Remi-C/modern_captain_bed/images/build_book_nomenclature/2015-09-30_09-45-54.png

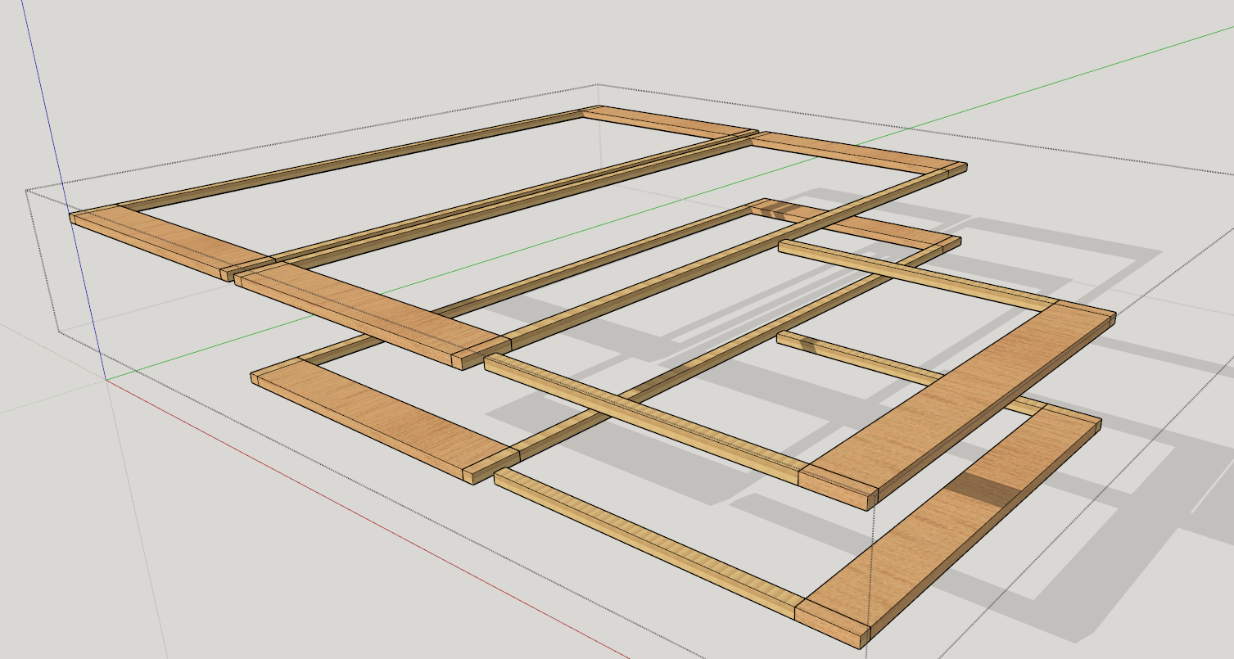
images/build_book_nomenclature/2015-09-30_09-45-54.png
