Remi-C/modern_captain_bed/images/build_book_nomenclature/A_2.png

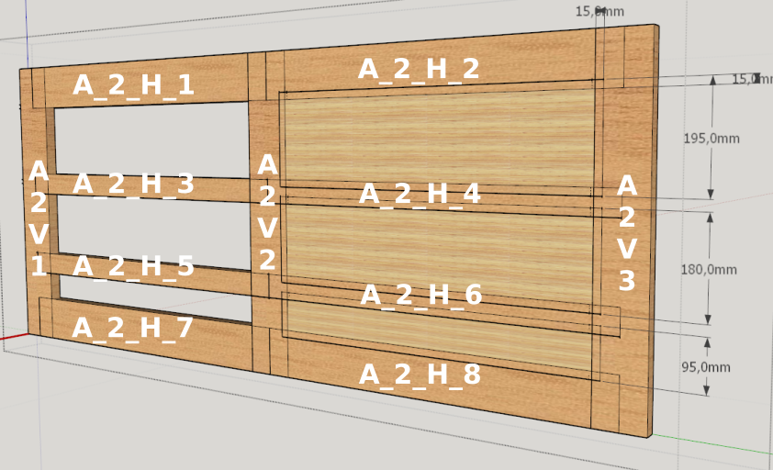
images/build_book_nomenclature/A_2.png
