Remi-C/modern_captain_bed/images/build_book_nomenclature/A_P_G.png

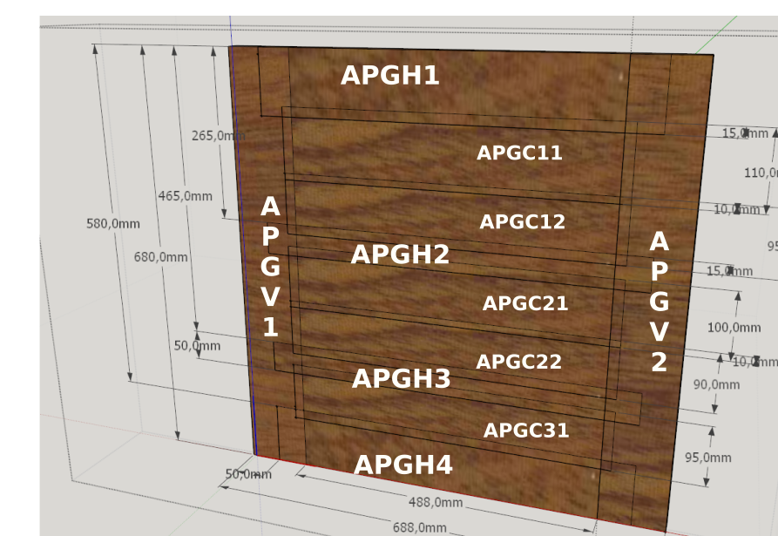
images/build_book_nomenclature/A_P_G.png
