Remi-C/modern_captain_bed/images/build_book_nomenclature/A_P_M.png

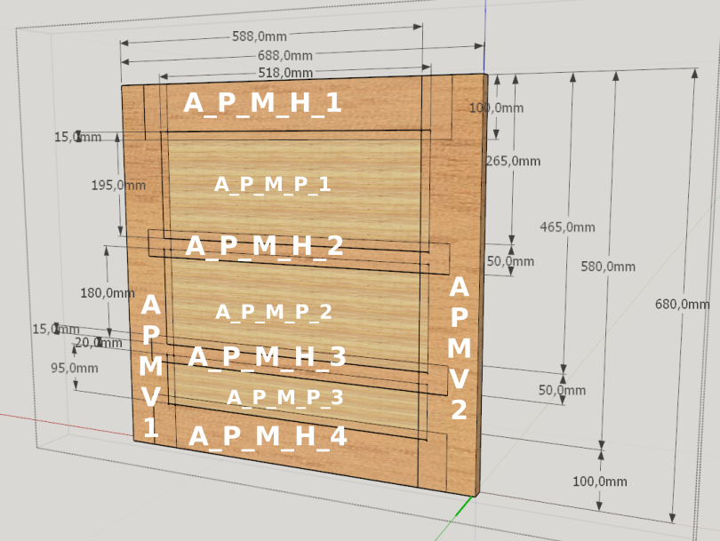
images/build_book_nomenclature/A_P_M.png
