Remi-C/modern_captain_bed/images/build_book_nomenclature/A_PI.png

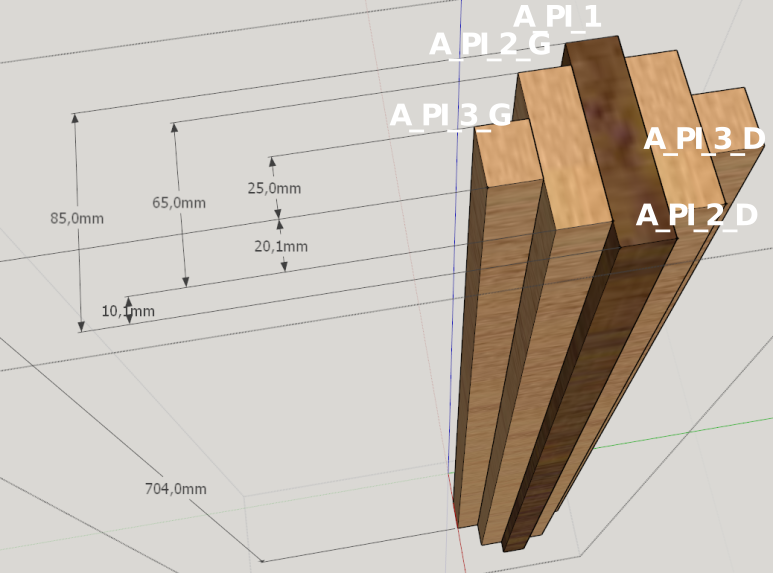
images/build_book_nomenclature/A_PI.png
