Remi-C/modern_captain_bed/images/build_book_nomenclature/A_T_P_thumbnail.jpeg

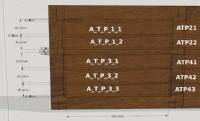
images/build_book_nomenclature/A_T_P_thumbnail.jpeg
