Remi-C/modern_captain_bed/images/bed_at_woodshop/assembly_at_woodshop (2).JPG

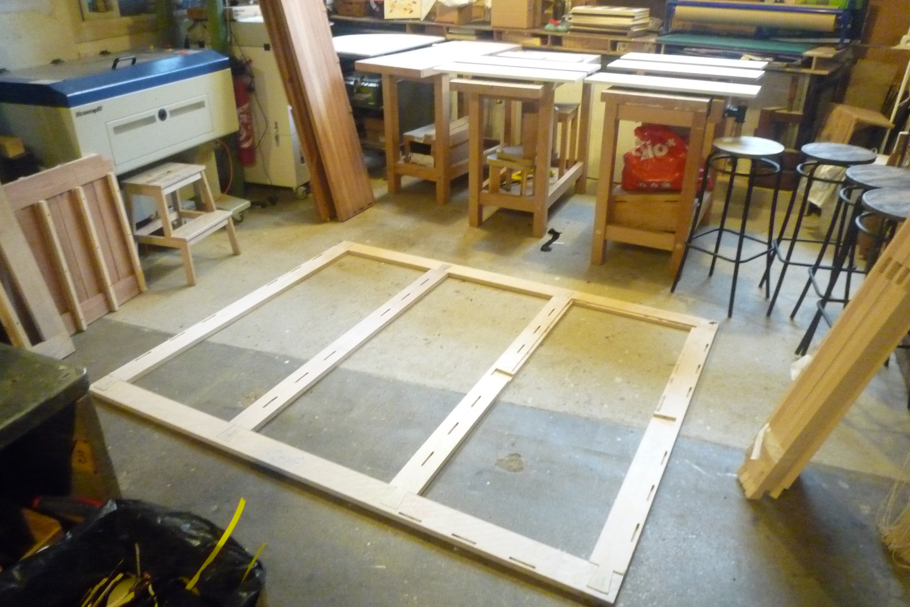
images/bed_at_woodshop/assembly_at_woodshop (2).JPG
