Remi-C/modern_captain_bed/images/bed_at_woodshop/assembly_at_woodshop (15)_thumbnail.jpeg

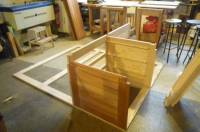
images/bed_at_woodshop/assembly_at_woodshop (15)_thumbnail.jpeg
