Remi-C/modern_captain_bed/images/build_book_nomenclature/lit_aux_dim.skp_-_SketchUp_Make_2015-09-30_09-24-27.png

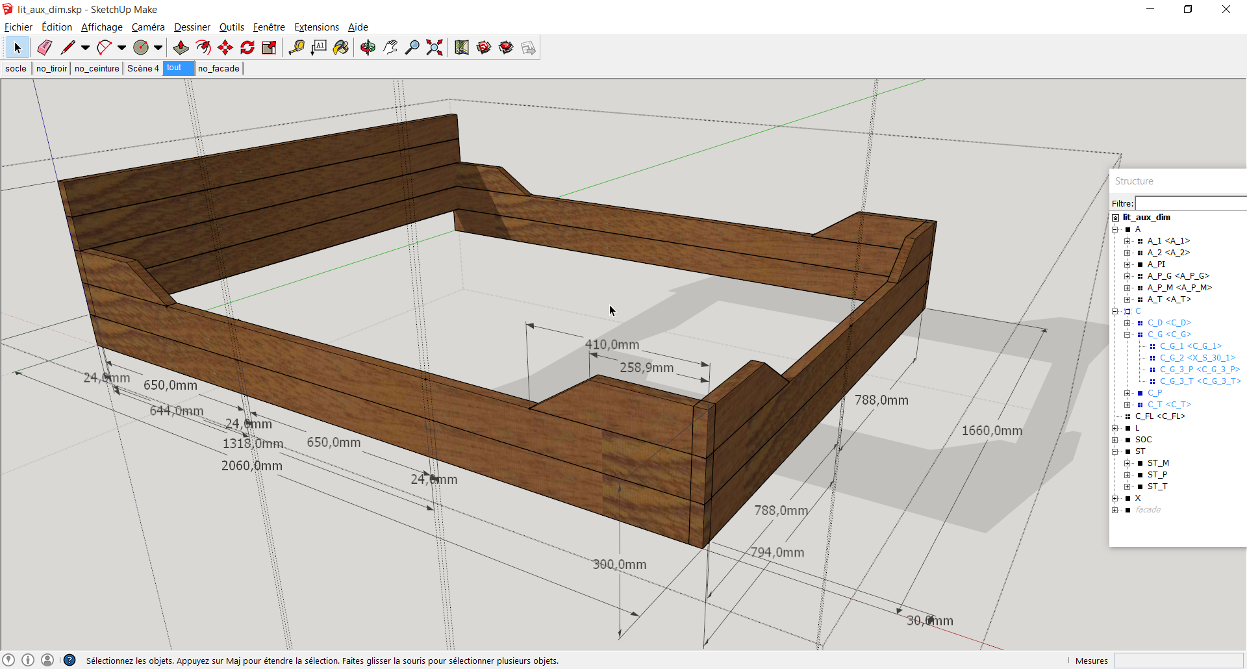
images/build_book_nomenclature/lit_aux_dim.skp_-_SketchUp_Make_2015-09-30_09-24-27.png
