Remi-C/modern_captain_bed/images/design/assemblage cloison.png

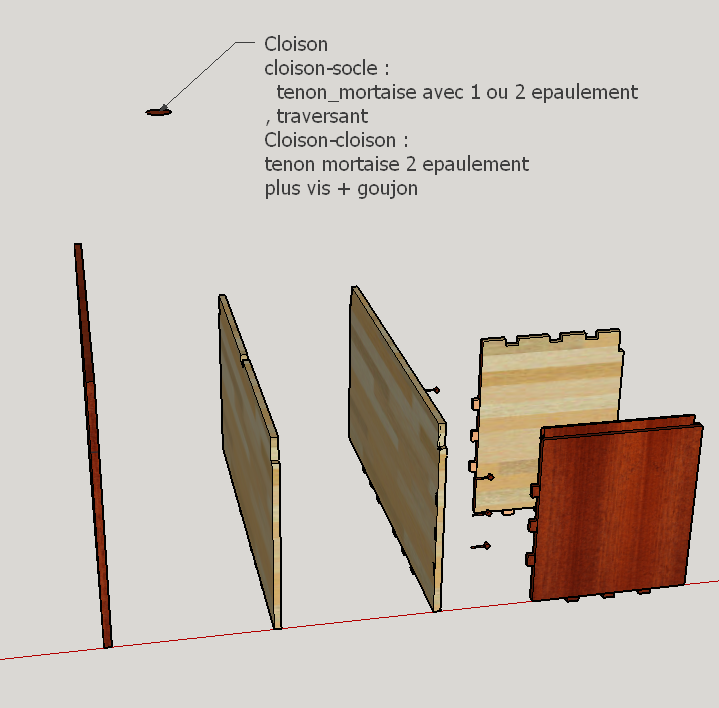
images/design/assemblage cloison.png
